paulomach/TG-II/report/imagens/Imagem006.jpg

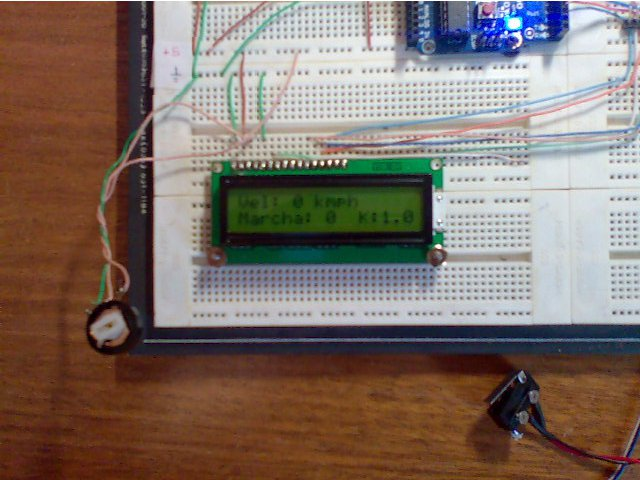
report/imagens/Imagem006.jpg
