paulomach/TG-II/report/imagens/Imagem007.jpg

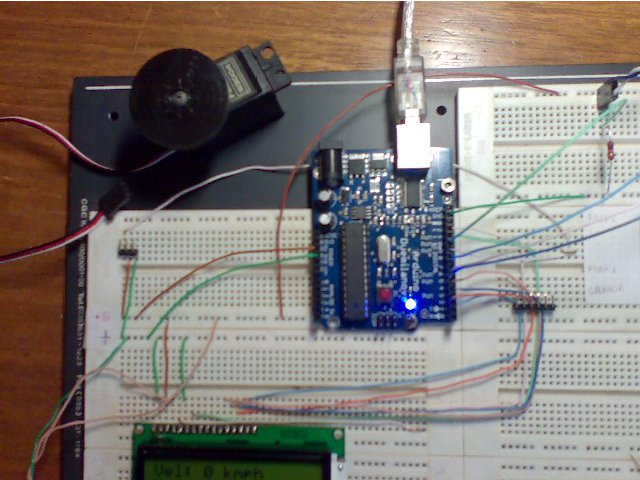
report/imagens/Imagem007.jpg
