paulomach/TG-II/report/imagens/Imagem008.jpg

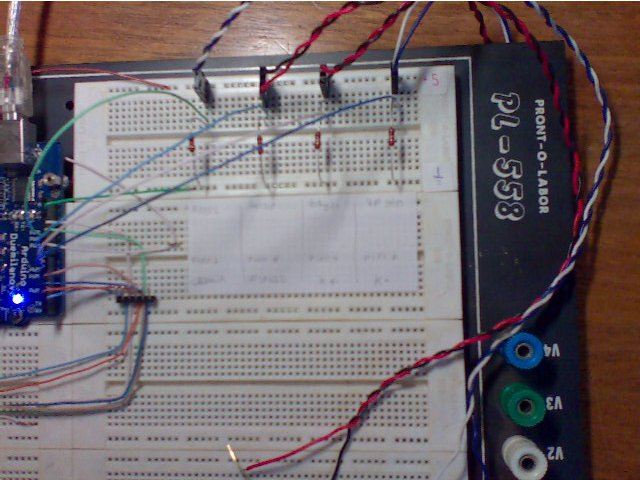
report/imagens/Imagem008.jpg
