paulomach/TG-II/report/imagens/Imagem009.jpg

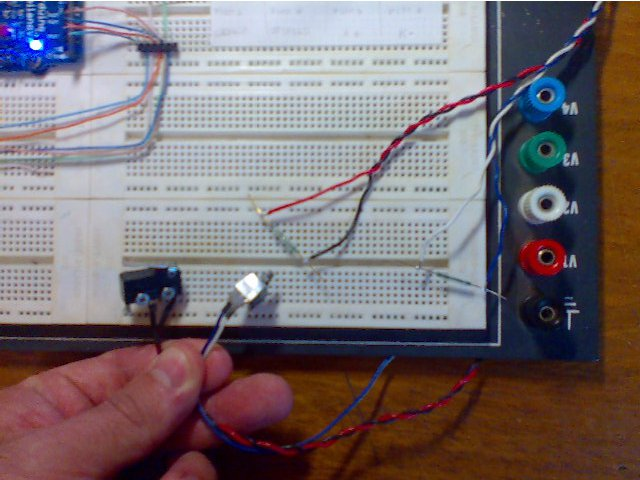
report/imagens/Imagem009.jpg
