paulomach/TG-II/report/imagens/plat.png

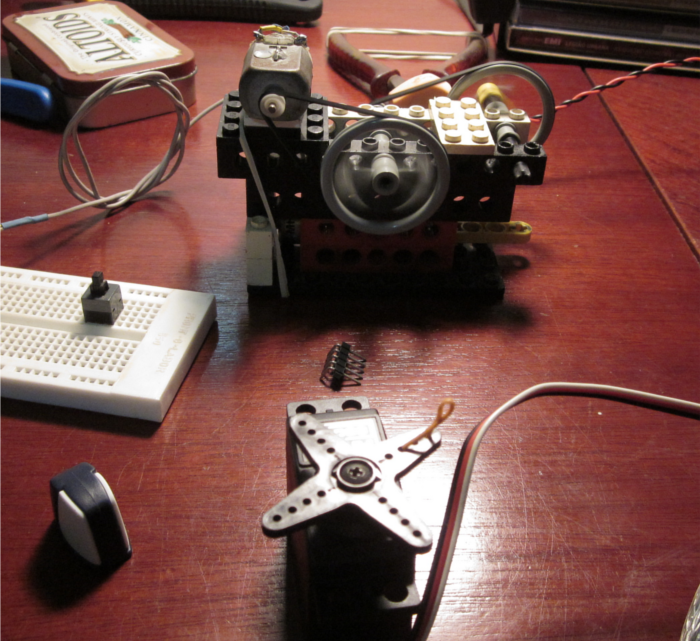
report/imagens/plat.png
