paulomach/TG-II/report/imagens/reed1.jpg

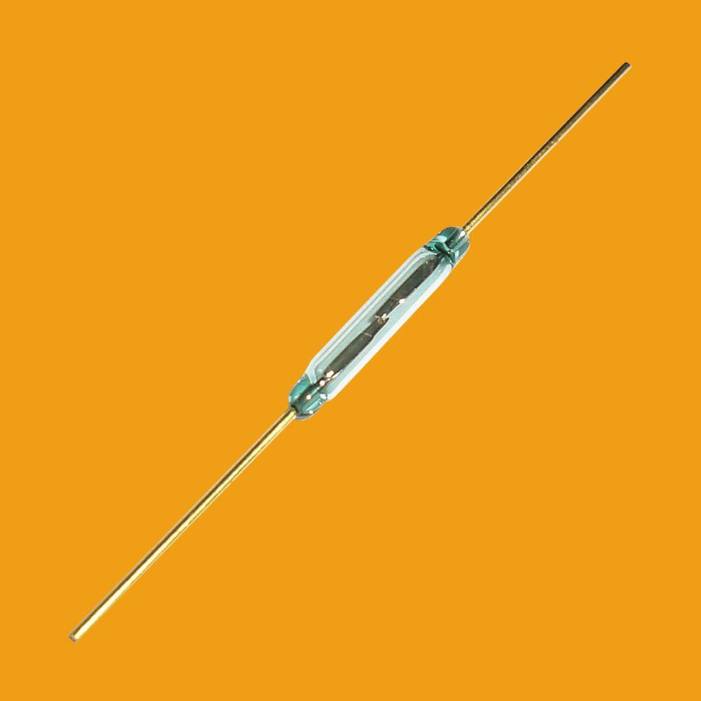
report/imagens/reed1.jpg
