paulomach/TG-II/report/imagens/reed2.jpg

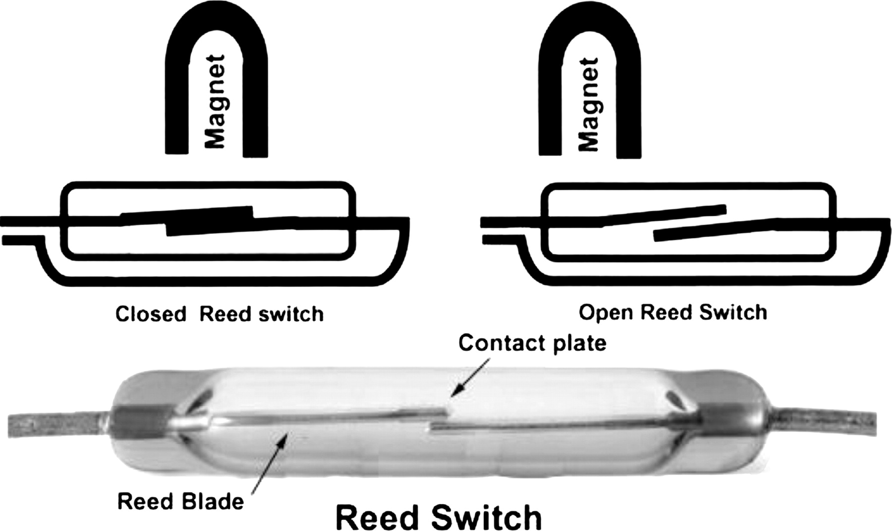
report/imagens/reed2.jpg
