paulomach/TG-II/report/imagens/reedok.jpg

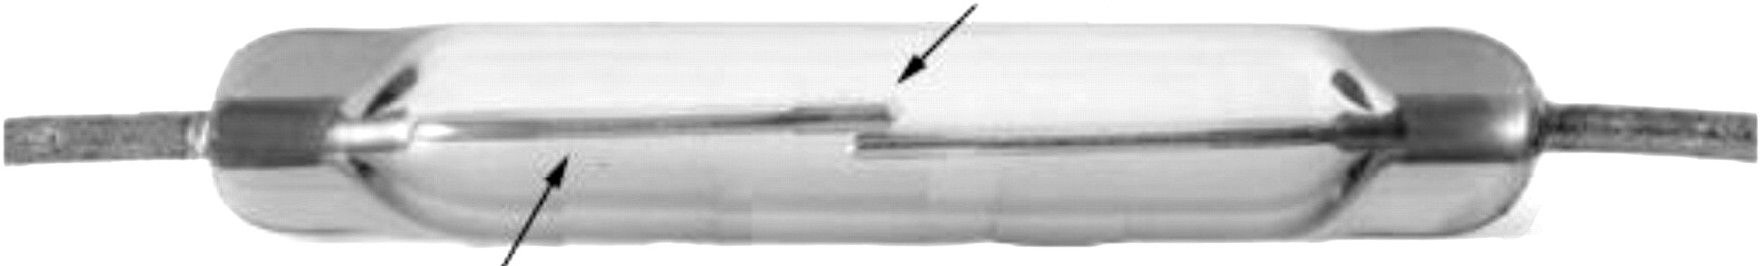
report/imagens/reedok.jpg
