paulomach/TG-II/report/imagens/S3004.jpg

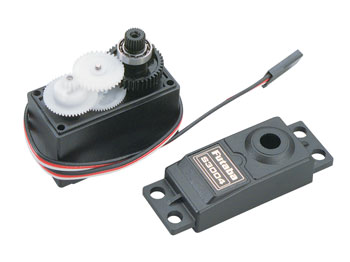
report/imagens/S3004.jpg
