paulomach/TG-II/report/imagens/making1.jpg

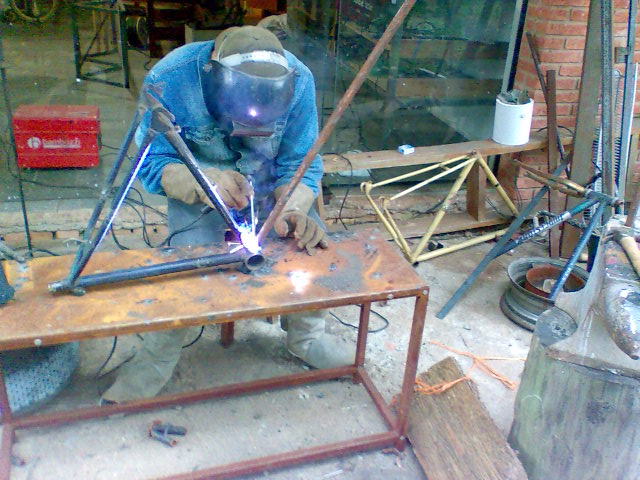
report/imagens/making1.jpg
