paulomach/TG-II/report/imagens/making2.jpg

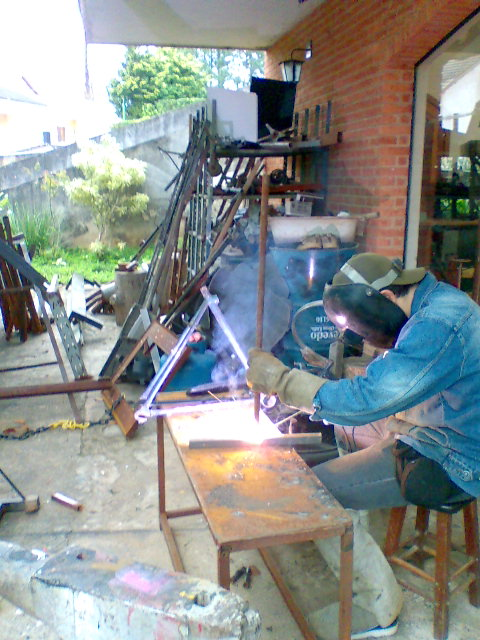
report/imagens/making2.jpg
