paulomach/TG-II/report/imagens/making3.jpg

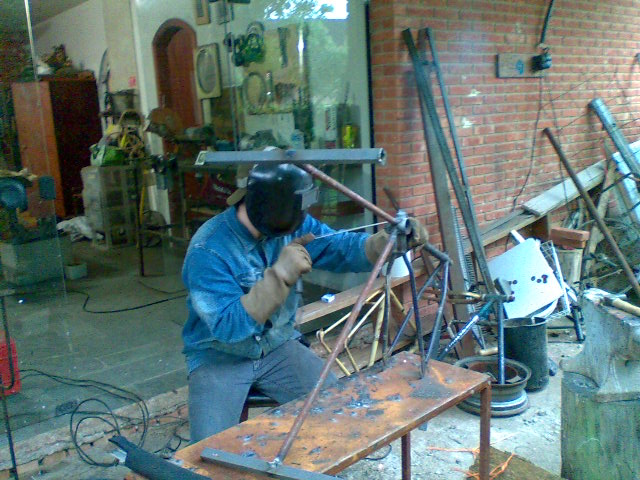
report/imagens/making3.jpg
